m24h/heatgun/circuit/gun.png

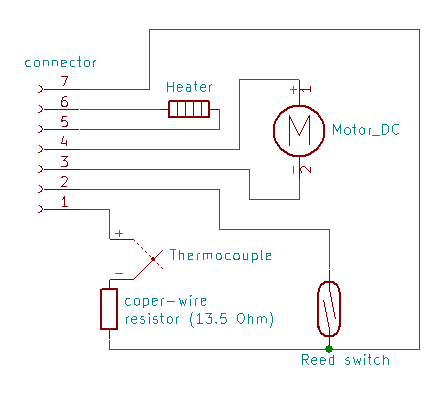
circuit/gun.png
