m24h/heatgun/circuit/output/3d.png

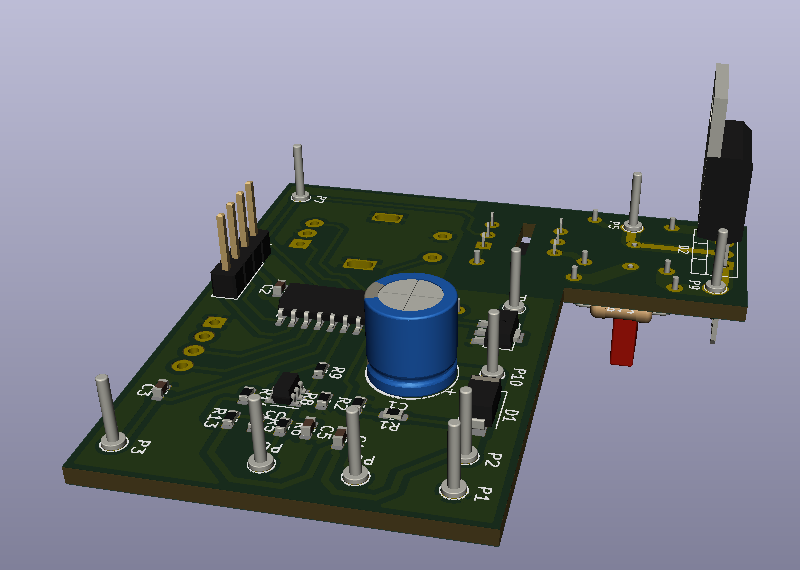
circuit/output/3d.png
