m24h/heatgun/circuit/output/pcb_b.png

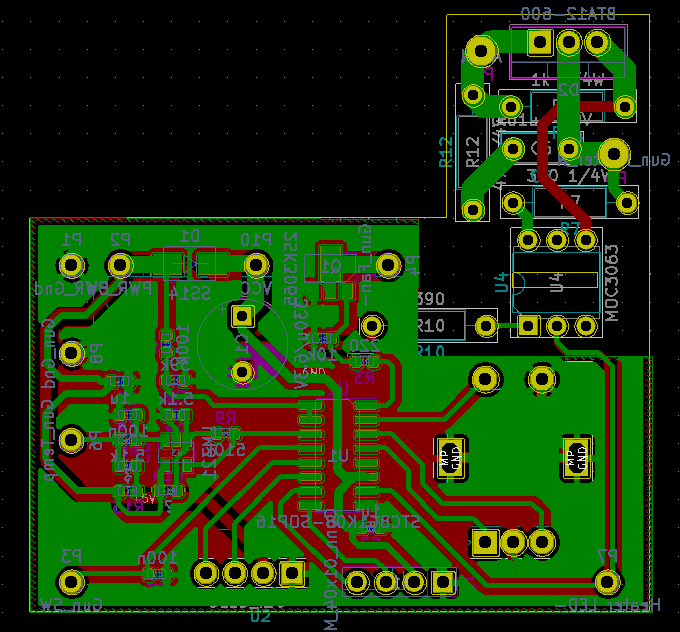
circuit/output/pcb_b.png
