m24h/heatgun/circuit/output/pcb_f.png

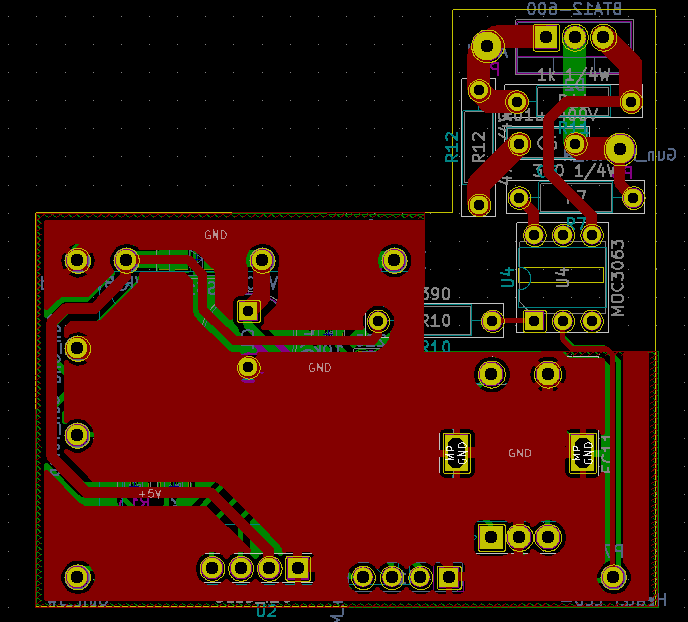
circuit/output/pcb_f.png
