m24h/heatgun/circuit/output/sch.png

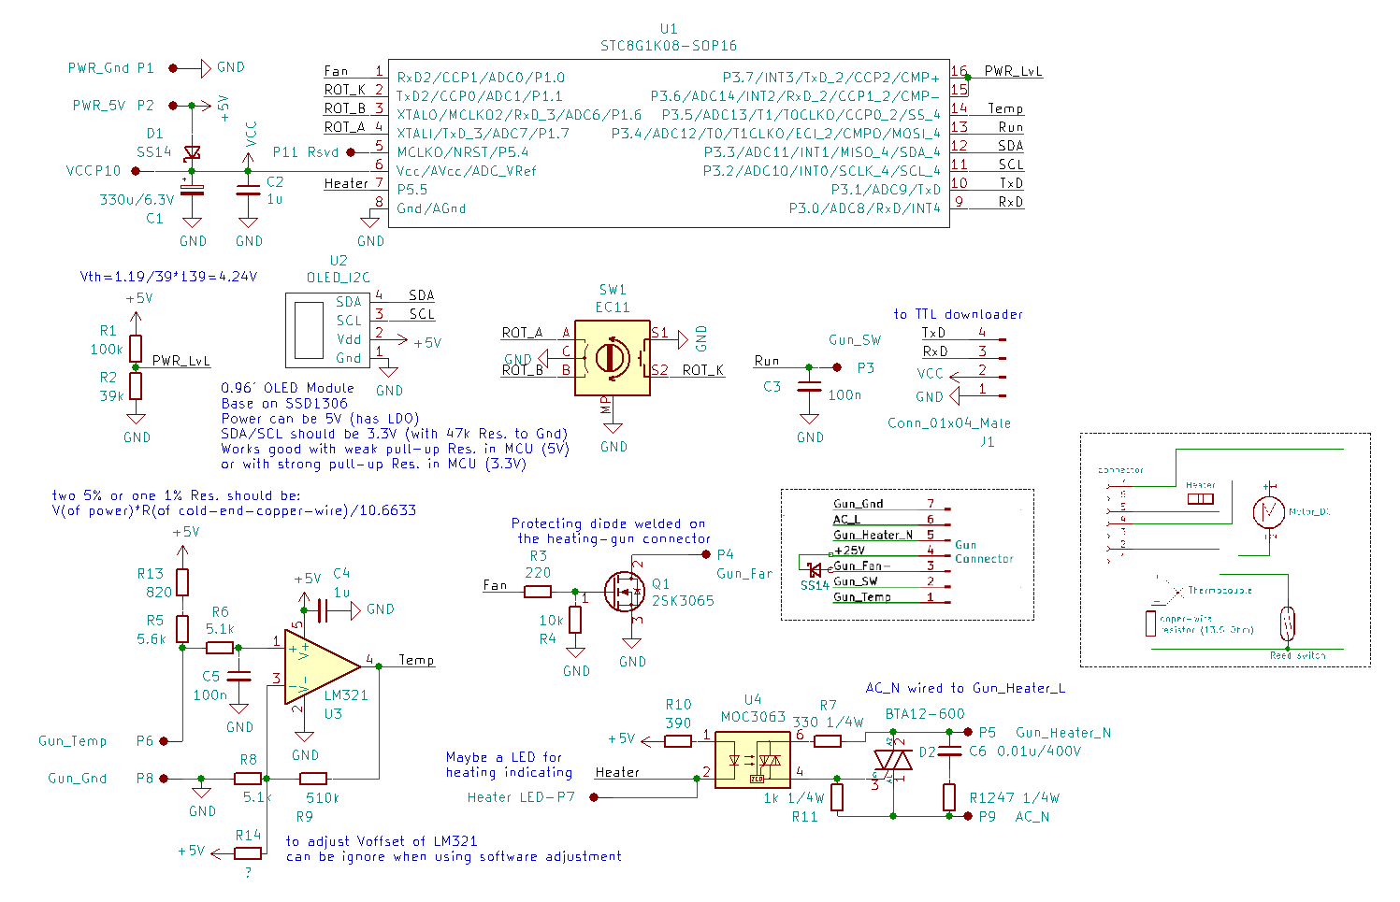
circuit/output/sch.png
