m24h/heatgun/practice/858-handle.jpg

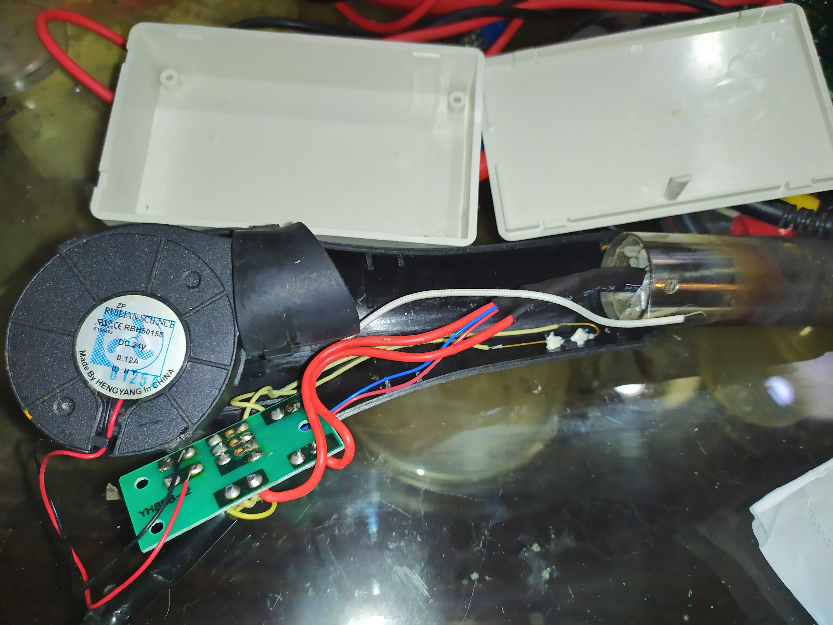
practice/858-handle.jpg
