m24h/heatgun/practice/burn1.png

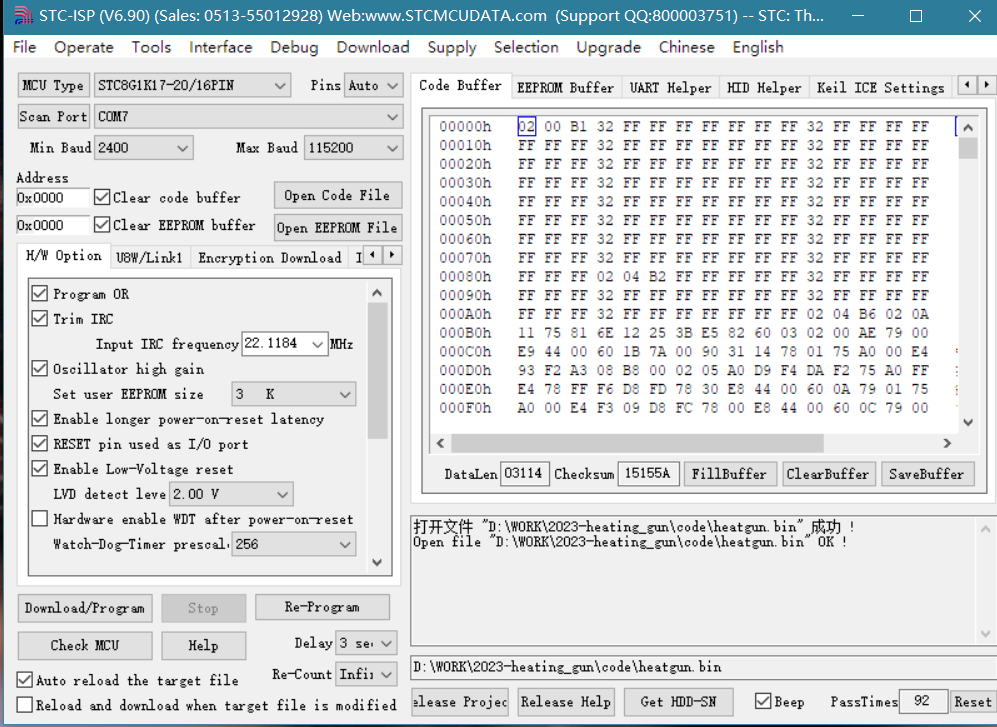
practice/burn1.png
