m24h/heatgun/practice/coper-wire-resistor.jpg

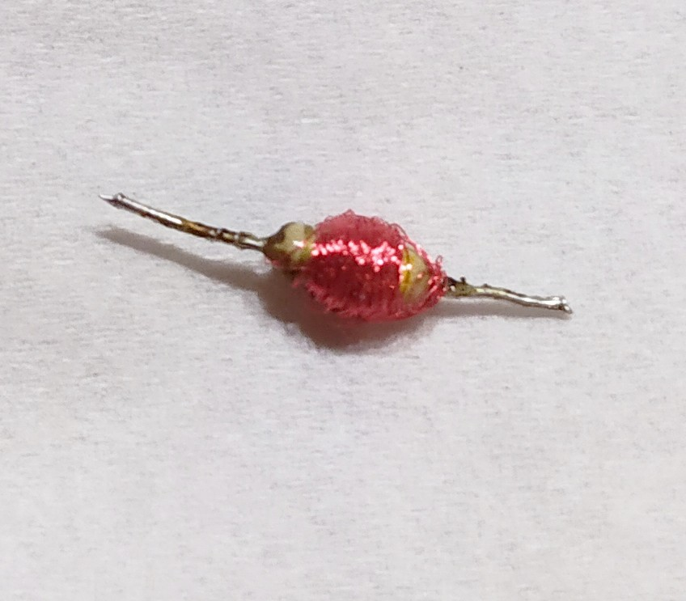
practice/coper-wire-resistor.jpg
