m24h/heatgun/practice/face.jpg

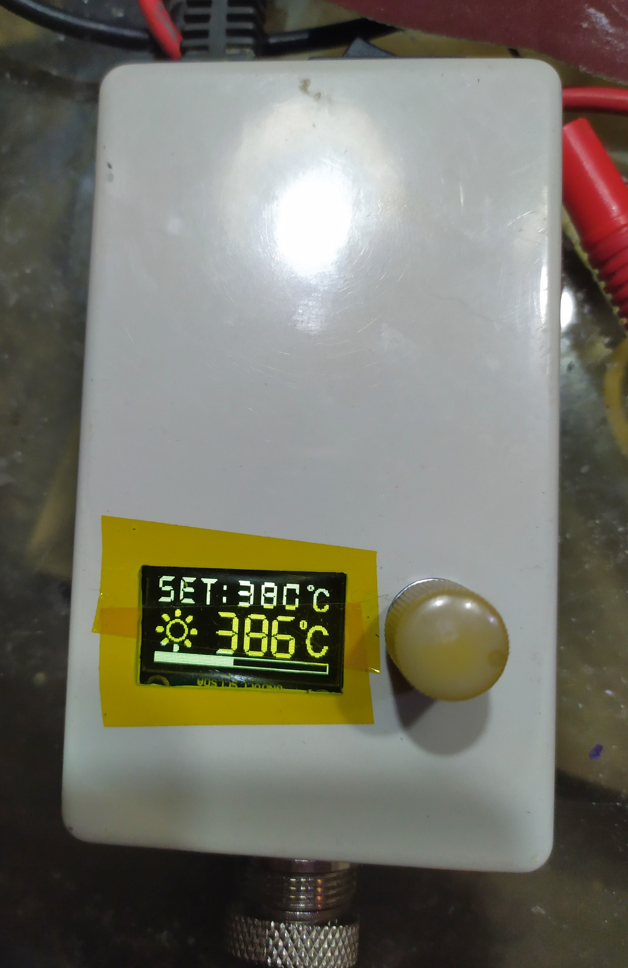
practice/face.jpg
