m24h/heatgun/practice/fan_pwm.jpg

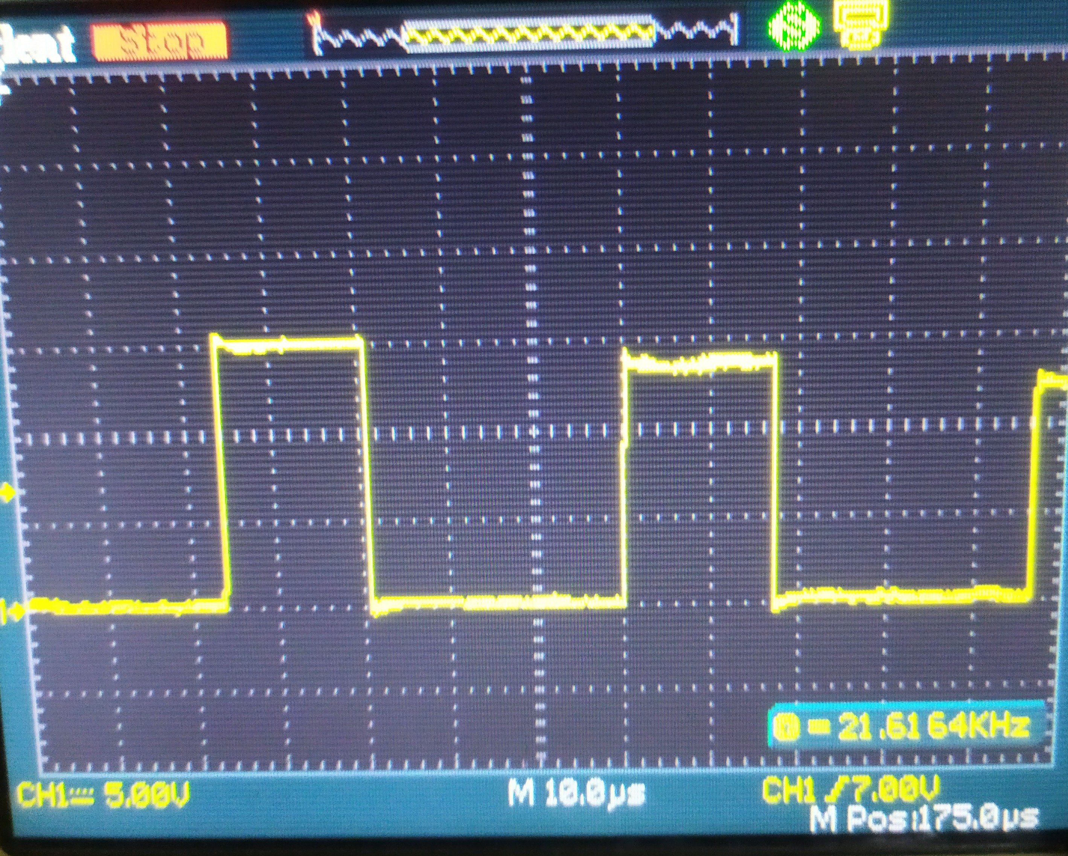
practice/fan_pwm.jpg
