m24h/heatgun/practice/handle-with-coper-wire-resistor.jpg

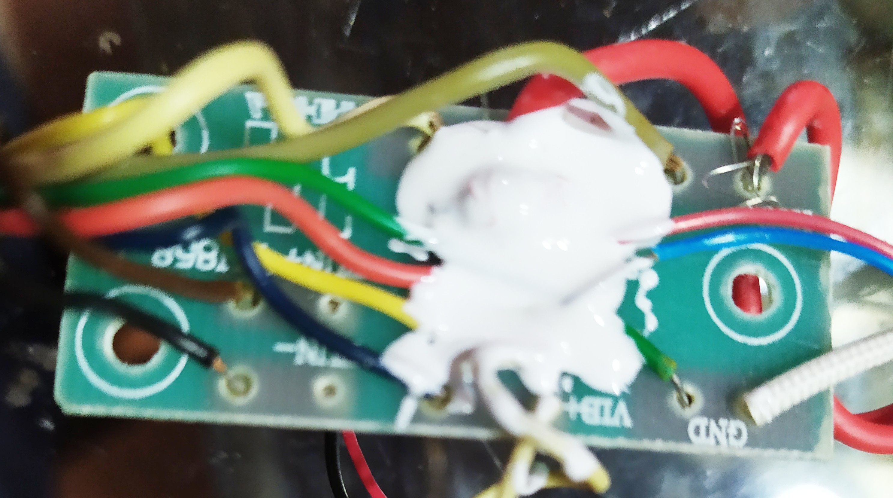
practice/handle-with-coper-wire-resistor.jpg
