m24h/heatgun/practice/pcb-bottom.jpg

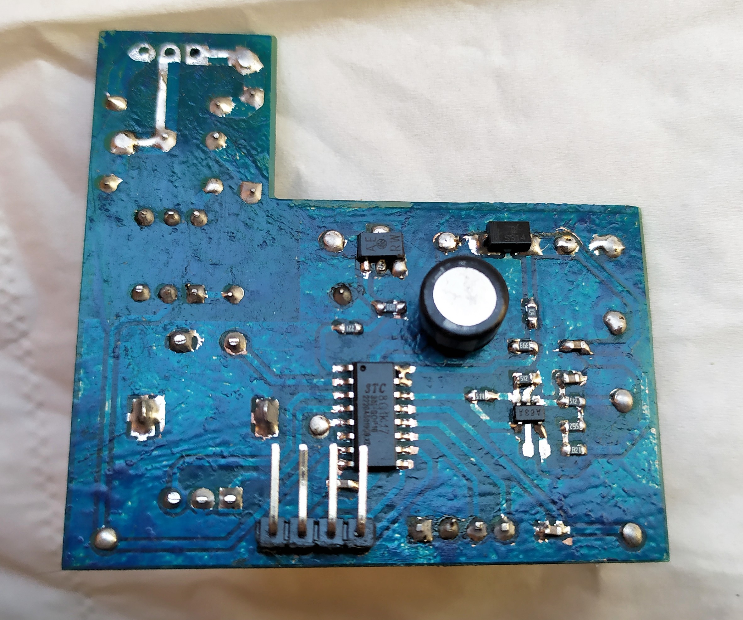
practice/pcb-bottom.jpg
