m24h/heatgun/practice/pcb-top.jpg

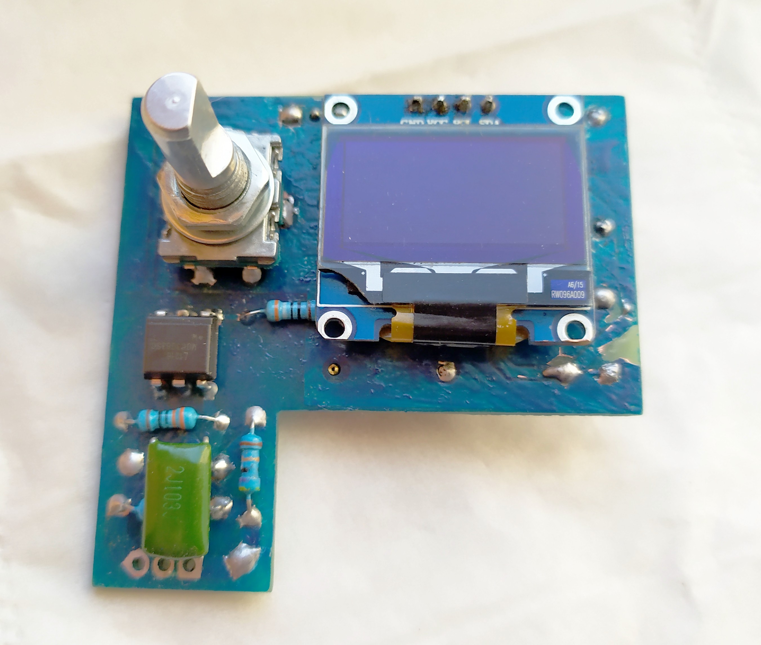
practice/pcb-top.jpg
