m24h/heatgun/practice/pid.png

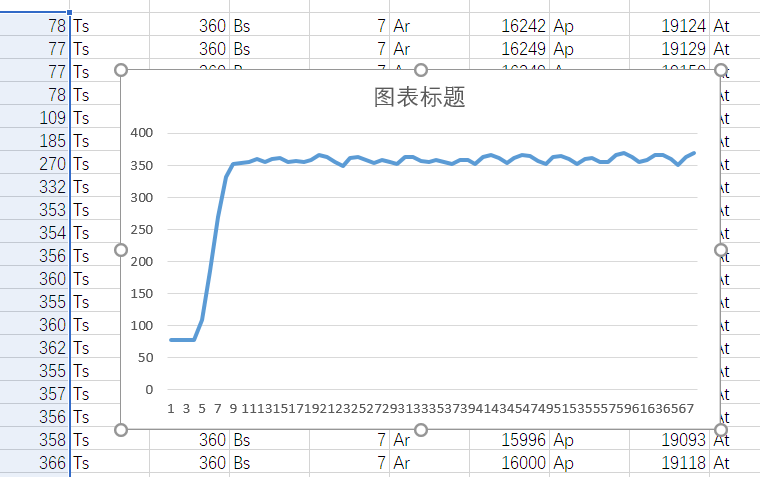
practice/pid.png
