m24h/heatgun/practice/power-transformer2.jpg

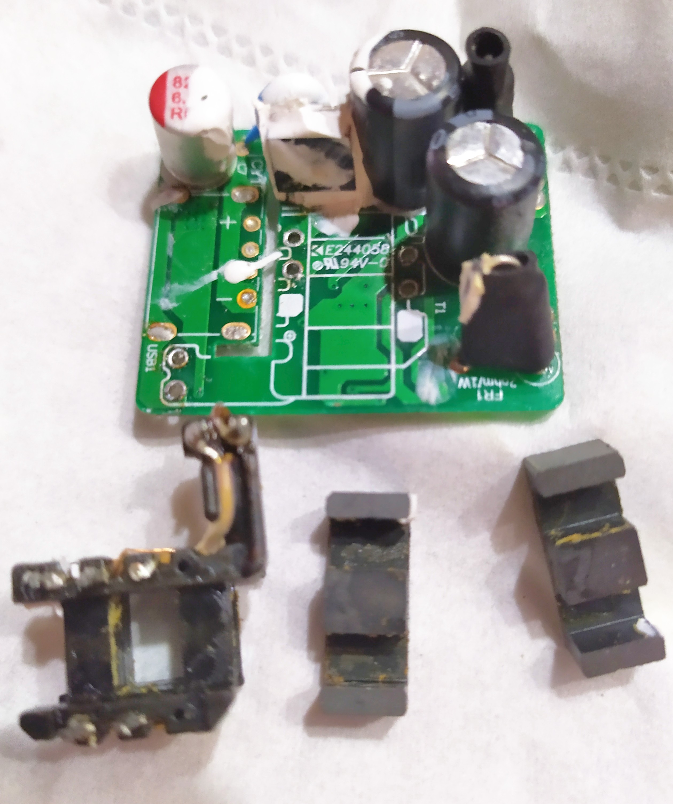
practice/power-transformer2.jpg
