m24h/heatgun/practice/power-transformer-remake.jpg

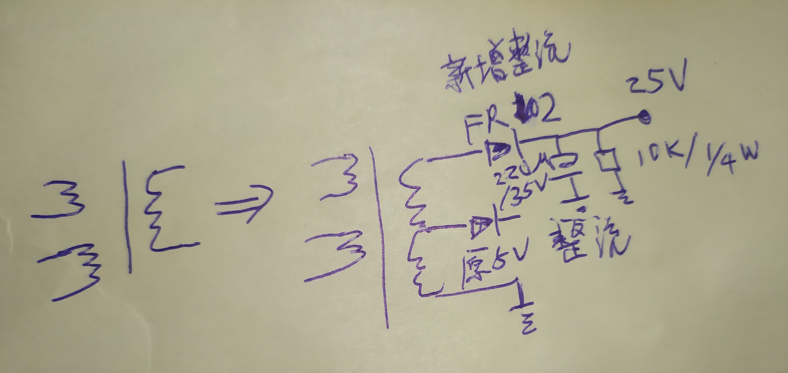
practice/power-transformer-remake.jpg
