m24h/heatgun/practice/power-transformer.jpg

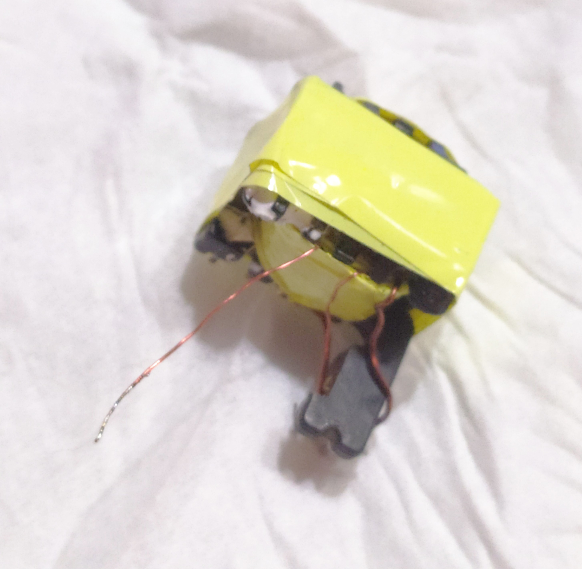
practice/power-transformer.jpg
