m24h/heatgun/code/K.c

// Copyright 2003 m24h, see http://www.apache.org/licenses/LICENSE-2.0

#include "K.h"

// a table of uV/256 => Temp*32 ,  in Celsius degree
__code u16 K_TEMP_FP5[]={
0,
207,
412,
616,
819,
1021,
1221,
1421,
1620,
1818,
2016,
2214,
2411,
2608,
2806,
3003,
3201,
3399,
3598,
3797,
3997,
4198,
4400,
4602,
4805,
5009,
5214,
5418,
5623,
5829,
6034,
6239,
6444,
6650,
6853,
7058,
7261,
7464,
7666,
7869,
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

// get temperature in 1/32 Celsius degree (5bit fixed-point) of K-thermocouple with input in uV
// return 0xFFFF when out of range
u16 K_temp(u16 uv) 
{
	u8 u=uv>>8;
	u8 v=(u8)uv;
		
	if (u>(u8)(sizeof(K_TEMP_FP5)/2-2))
		return 0xffff;

	u16 a=K_TEMP_FP5[u];
	u8 k=(u8)K_TEMP_FP5[++u] - (u8)a;   // intervals of neighbor elements in K_TEMP32 are less then 256
	return (u8)((k*v+128)>>8)+a; // SDCC follows ANSI C rule : 8bit * 8bit => int * int, then for optimization, op. MUL, not _mulint(), will be used here by SDCC
}

// get uV from temperature, input temperature is in 1/32 Celsius degree (5bit fixed-point)
// return 0xFFFF when out of range
u16 K_uv(u16 temp)
{
	if (K_TEMP_FP5[sizeof(K_TEMP_FP5)/2-1]<temp)
		return 0xFFFF;
	
	u8 u=1;
	u16 a=0;
	u16 b;
	do {
		b=K_TEMP_FP5[u];
		if (b>=temp)
			break;
		a=b;
		u++;
	} while (1);	
	u8 k=(u8)(b-a);
	return ((u16)(u-1)<<8)+((((u16)(temp-a)<<8)+(k>>1))/k);
}
